AlexandreD-Maker/robotic-arm/electronics/circuit_diagram.kicad_sch

## KiCad design electronics/circuit_diagram.kicad_sch (2026-01-15)

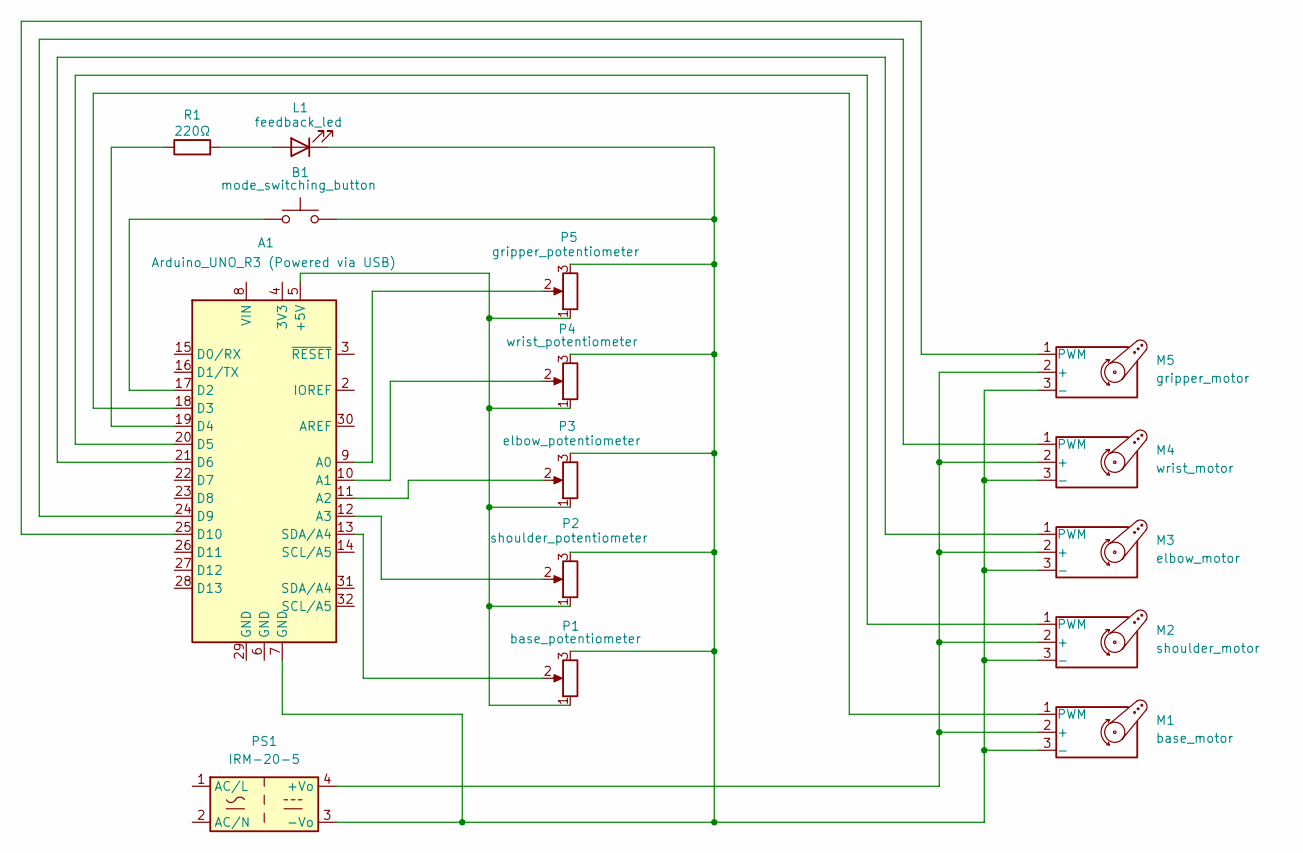
[picture p8: schematic circuit_diagram.kicad_sch]

Parts:
A1: Arduino_UNO_R3 (Powered via USB); Arduino_UNO_R3
B1: mode_switching_button
L1: feedback_led
M1: base_motor
M2: shoulder_motor
M3: elbow_motor
M4: wrist_motor
M5: gripper_motor
P1: base_potentiometer
P2: shoulder_potentiometer
P3: elbow_potentiometer
P4: wrist_potentiometer
P5: gripper_potentiometer
PS1: IRM-20-5; Converter_ACDC_MeanWell_IRM-20-xx_THT
R1: 220Ω

Connections:
unnamed: A1.5 (+5V), P1.1, P2.1, P3.1, P4.1, P5.1
unnamed: A1.7 (GND), B1.2, L1.1 (K), M1.3 (-), M2.3 (-), M3.3 (-), M4.3 (-), M5.3 (-), P1.3, P2.3, P3.3, P4.3, P5.3, PS1.3 (-Vo)
unnamed: A1.9 (A0), P5.2
unnamed: A1.10 (A1), P4.2
unnamed: A1.11 (A2), P3.2
unnamed: A1.12 (A3), P2.2
unnamed: A1.13 (SDA/A4), P1.2
unnamed: A1.17 (D2), B1.1
unnamed: A1.18 (D3), M1.1 (PWM)
unnamed: A1.19 (D4), R1.1
unnamed: A1.20 (D5), M2.1 (PWM)
unnamed: A1.21 (D6), M3.1 (PWM)
unnamed: A1.24 (D9), M4.1 (PWM)
unnamed: A1.25 (D10), M5.1 (PWM)
unnamed: L1.2 (A), R1.2
unnamed: M1.2 (+), M2.2 (+), M3.2 (+), M4.2 (+), M5.2 (+), PS1.4 (+Vo)
